MattisLind/DECNA-replica/Kicad/DECNA-replica/DECNA-replica.kicad_pcb

## KiCad design automation/automation.kicad_sch

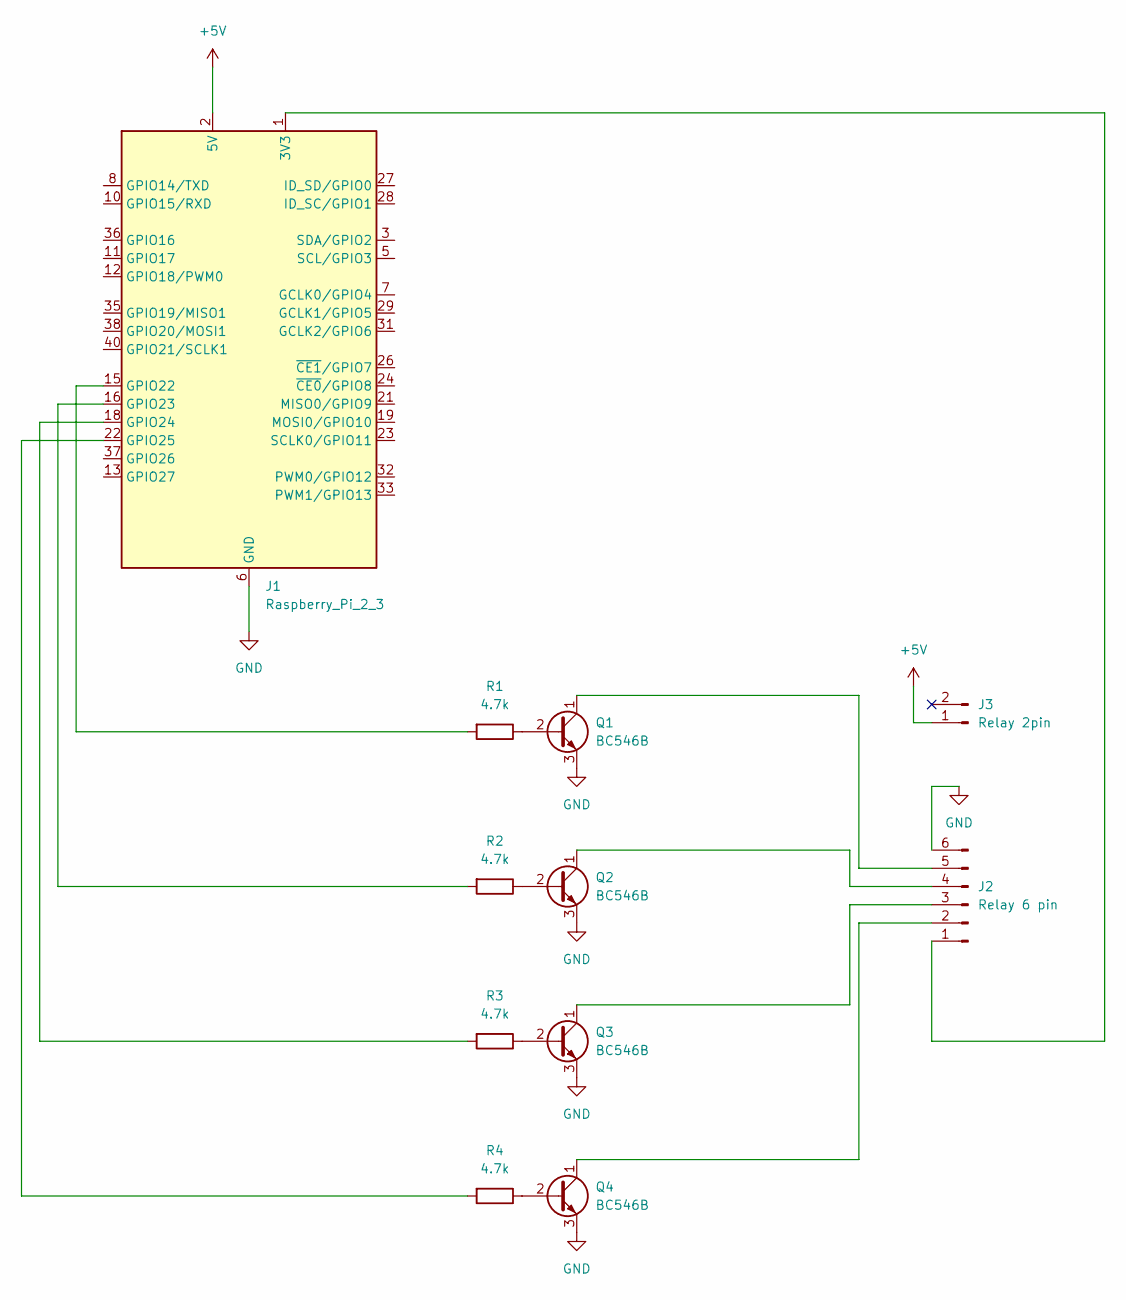
[picture p7: schematic automation.kicad_sch]

Parts:
J1: Raspberry_Pi_2_3
J2: Relay 6 pin
J3: Relay 2pin
Q1, Q2, Q3, Q4: BC546B; TO-92_Inline
R1, R2, R3, R4: 4.7k

Connections:
+5V: J1.2 (5V), J1.4 (5V), J3.1
GND: J1.6 (GND), J1.9 (GND), J1.14 (GND), J1.20 (GND), J1.25 (GND), J1.30 (GND), J1.34 (GND), J1.39 (GND), J2.6, Q1.3 (E), Q2.3 (E), Q3.3 (E), Q4.3 (E)
unnamed: J1.1 (3V3), J1.17 (3V3), J2.1
unnamed: J1.15 (GPIO22), R1.2
unnamed: J1.16 (GPIO23), R2.2
unnamed: J1.18 (GPIO24), R3.2
unnamed: J1.22 (GPIO25), R4.2
unnamed: J2.2, Q4.1 (C)
unnamed: J2.3, Q3.1 (C)
unnamed: J2.4, Q2.1 (C)
unnamed: J2.5, Q1.1 (C)
unnamed: Q1.2 (B), R1.1
unnamed: Q2.2 (B), R2.1
unnamed: Q3.2 (B), R3.1
unnamed: Q4.2 (B), R4.1
